tealvince/OBDGauge/src/arduino/ModularOBDGauge/VSettings.h

#ifndef _VSETTINGS
#define _VSETTINGS

#include "VMenu.h"

///////////////////////////////////////////////////////////////
// VSETTINGS.H
// Settings menu
///////////////////////////////////////////////////////////////

struct SettingsDataSource {
  void (*clearHistory)(void);
  void (*clearDistance)(void);
  void (*clearFuel)(void);
  void (*clearTime)(void);
  void (*adjustDistance)(void);
  void (*adjustFuel)(void);
  void (*adjustTime)(void);
  void (*setBrightness)(int brightness);
  void (*toggleCurrentItemUnits)(void);
  void (*setAllCurrentItemUnits)(bool);
  void (*autoScanItems)(void);
  void (*hideCurrentItem)(void);
  void (*showItemByName)(char *name);
  void (*showCurrentItemDetails)(void);
  void (*showDtcMonitors)(void);
  void (*showDtcCodes)(void);
  void (*clearDtcCodes)(void);
  void (*setFuelAdjustment)(void);
  void (*setKgWeight)(void);
  void (*startGearDetect)(void);
  int  (*getGearCount)(void);
  void (*showGears)(void);
  void (*addGear)(void);
  void (*removeGear)(void);
  void (*editGear)(int);
  void (*toggleLoopMode)(void);
  void (*toggleDemoMode)(void);
  void (*toggleDebugMode)(void);
  void (*enterSniffMode)(int mode);

  bool (*isCurrentItemHidden)(void);
  bool (*isCurrentItemMultiUnit)(void);
  bool (*isCurrentItemComputed)(void);
  char *(*getCurrentItemAltUnits)(void);

  char **(*getHiddenItemTitles)(void); // null terminated list
  char **(*getHiddenItemUnits)(void);  // null terminated list
};

class VSettings {
  private:

  public:
    bool demoModeEnabled;
    bool debugModeEnabled;
    void setup(struct SettingsDataSource *dataSource, struct MenuDisplayProvider *display, struct MenuControlsProvider *controls);
    void showMenu();
};

#endif
