tealvince/OBDGauge/src/arduino/ModularOBDGauge/VSerial.h

///////////////////////////////////////////////////////////////
// VSERIAL.H
// Software-driven serial port
///////////////////////////////////////////////////////////////

#include "Environment.h"

#ifndef _VSERIAL
#define _VSERIAL

class VSerial {
  private:
    int inPin, outPin;
    unsigned long flips[SERIAL_MAX_FLIPS];
    unsigned char bytes[SERIAL_MAX_BYTES];

    int  readFlips(long *buffer, int buflen, long startTimeoutMs, long inactivityTimeoutMs);
    int  decodeFlipsToBytes(unsigned char *bytes, int bytesLen, unsigned long *flips, int flipCount, long baud, unsigned long *minByteSpacing, unsigned long *maxByteSpacing);
    int  decodeFlippedValueAtTime(unsigned long time, unsigned long *flips, int flipCount);
    void delayUntil(unsigned long waitUs);

  public:
    void setup(int inPin, int outPin, void (*smartDelay)(unsigned long));

    int  readBytes(unsigned char **byteBuf, unsigned long timeoutMs, unsigned long inactivityTimeoutMs, unsigned long baud, unsigned long *minByteSpacing, unsigned long *maxByteSpacing);
    int  readFlipIntervals(unsigned long **byteBuf, unsigned long timeoutMs, unsigned long inactivityTimeoutMs);
    void sendBytes(unsigned char *bytes, int count, unsigned long baud, int msDelayBetweenBytes);
    void sendByte(unsigned char val, unsigned long baud);
    void sendByteRepeatedly(unsigned char byte, int count, unsigned long baud, int msDelay);
    void sendBit(int val, long waitUs);
    void waitForIdle(unsigned long idleMs, unsigned long timeoutMs);
};

#endif
